Twometer/twometer-vr/TVR.Service/TVR.Service.Core/Resources/PSEye.yml

# Config file for the PlayStation 3 Eye camera

VideoSourceType: PSEye
VideoSourceIndex: 0
FrameWidth: 640
FrameHeight: 480
Framerate: 60
TransformConfig:
    PFocalLength: 622.72
    PixelsPerMeter: 523.80
ExposureConfig:
    Start: 75
    Limit: 0
    Step: -5
    WarmupFrames: 12
    CooldownFrames: 3
    StableFrames: 10
    MaximumChange: 0.5
    Threshold: 15
Distortion: [-0.10771770030260086, 0.1213262677192688, 0.04875476285815239, 0.00091733073350042105, 0.00010589254816295579]
UseAdaptiveBrightness: False
# TODO: https://dominoc925.blogspot.com/2016/04/using-emgucvopencv-to-correct-optical.html and https://github.com/caulifla/emgucv
