Twometer/twometer-vr/TVR.Driver/src/Utils/Constants.h

//
// Created by Twometer on 9 Dec 2020.
//

#ifndef TVR_DRIVER_CONSTANTS_H
#define TVR_DRIVER_CONSTANTS_H

#include <cstdint>

constexpr const char *SERVER_IP = "127.0.0.1";
constexpr uint16_t SERVER_PORT = 20156;
constexpr int MAX_PACKET_LEN = 4096;
constexpr uint32_t UNIVERSE_ID = 2688095746;

#endif //TVR_DRIVER_CONSTANTS_H
